xuehlcn/bilibili_weather_clock/取模软件/小电视动画1/xiaodianshi(2)_3.jpeg

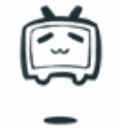
取模软件/小电视动画1/xiaodianshi(2)_3.jpeg
